OpenKNX/OpenKNX-KNeoPiX/Documentation/Renderings/rendered_case_Back.png

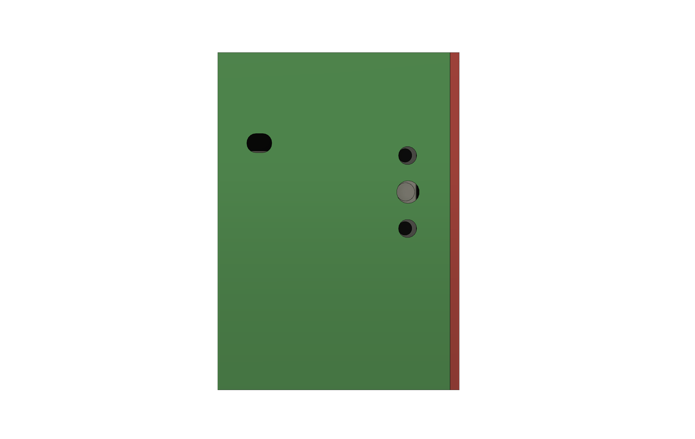
Documentation/Renderings/rendered_case_Back.png
