OpenKNX/OpenKNX-KNeoPiX/Documentation/Renderings/rendered_pcb_back.png

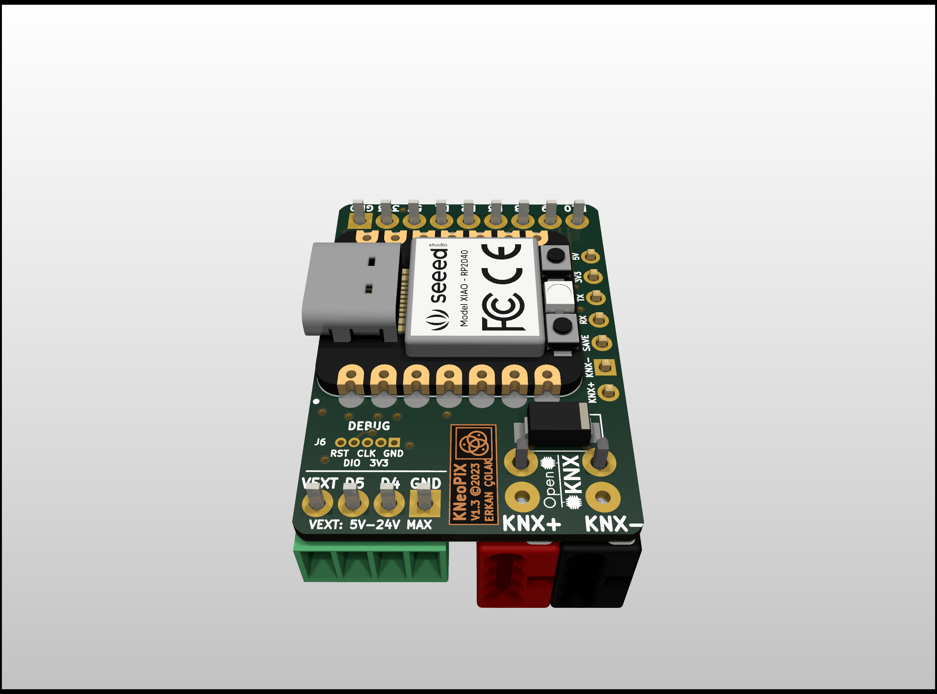
Documentation/Renderings/rendered_pcb_back.png
