OpenKNX/OpenKNX-KNeoPiX/Documentation/Renderings/rendered_pcb_bot.png

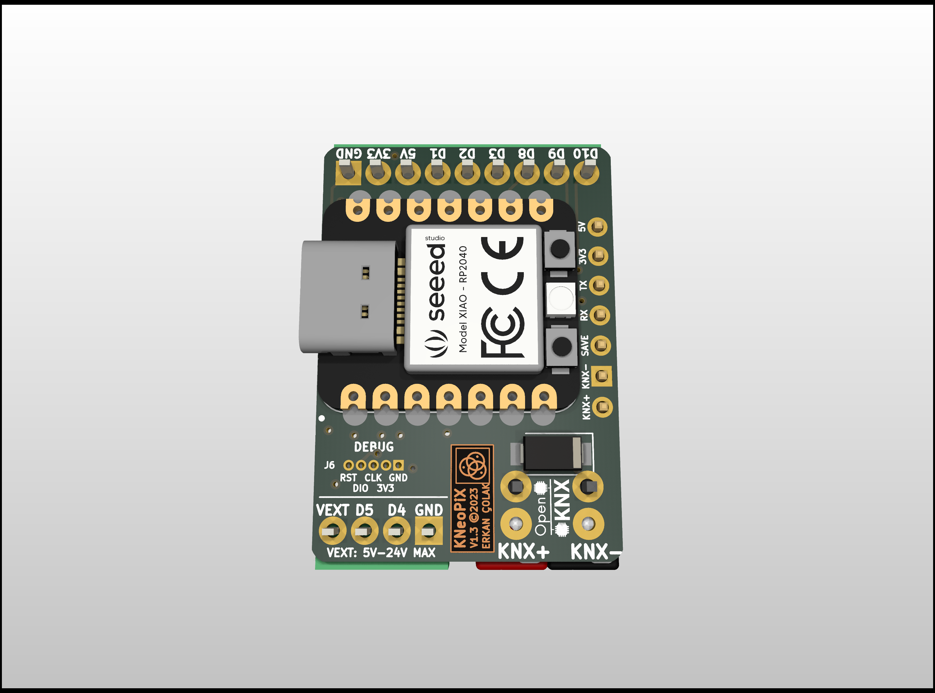
Documentation/Renderings/rendered_pcb_bot.png
