OpenKNX/OpenKNX-KNeoPiX/Documentation/Renderings/rendered_pcb_front.png

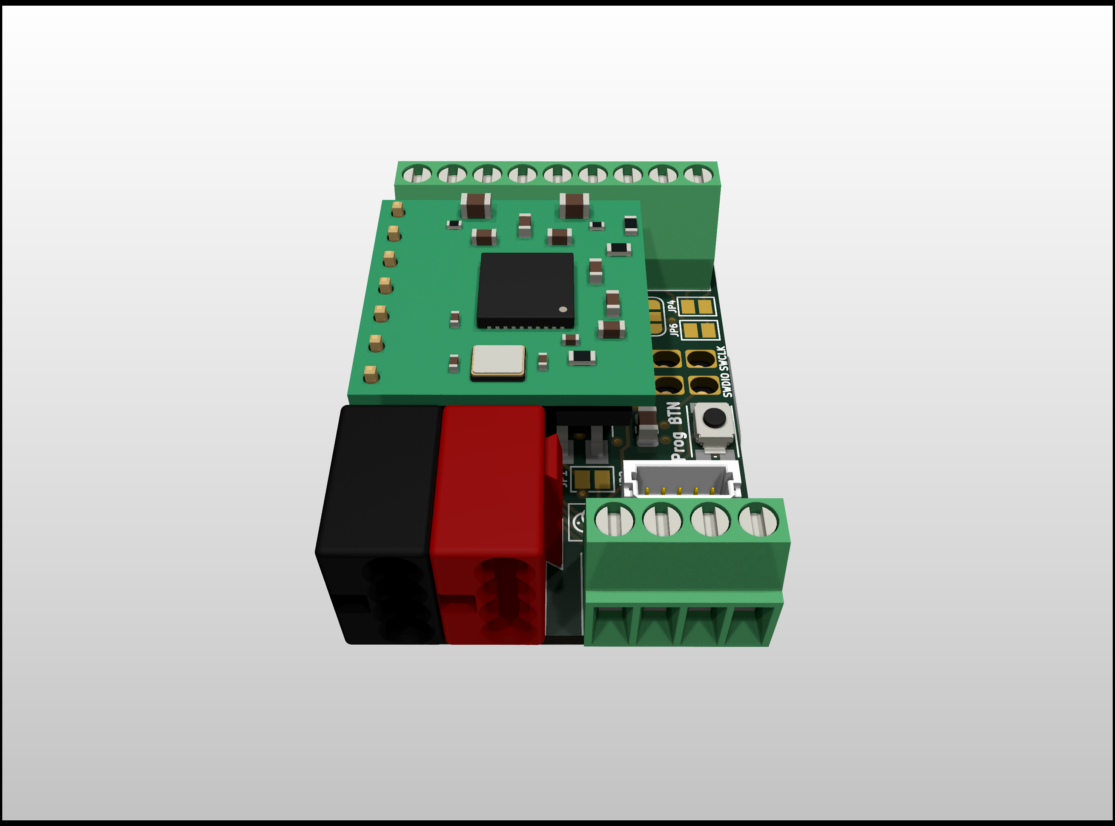
Documentation/Renderings/rendered_pcb_front.png
