OpenKNX/OpenKNX-KNeoPiX/Documentation/Renderings/rendered_pcb_l_back.png

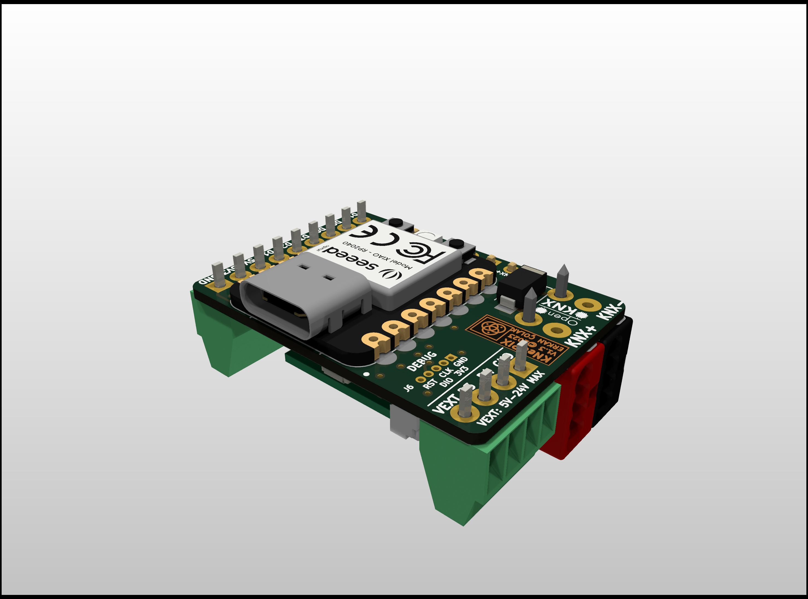
Documentation/Renderings/rendered_pcb_l_back.png
