OpenKNX/OpenKNX-KNeoPiX/Documentation/Renderings/rendered_pcb_l_front.png

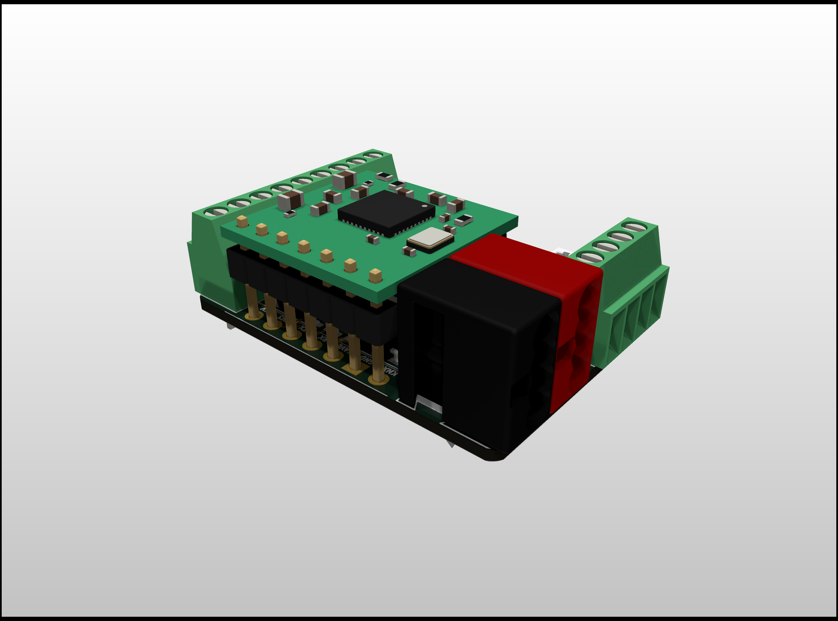
Documentation/Renderings/rendered_pcb_l_front.png
