OpenKNX/OpenKNX-KNeoPiX/Documentation/Renderings/rendered_pcb_r_back.png

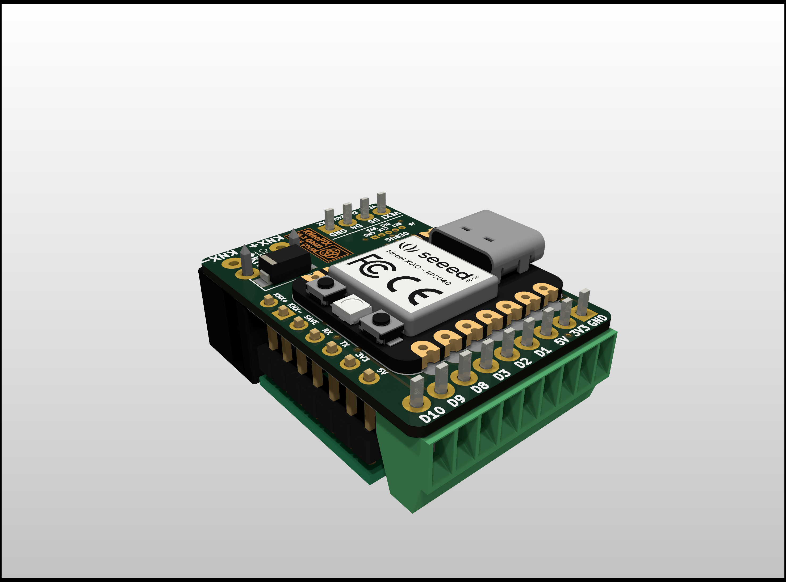
Documentation/Renderings/rendered_pcb_r_back.png
