OpenKNX/OpenKNX-KNeoPiX/Documentation/Renderings/rendered_pcb_r_front.png

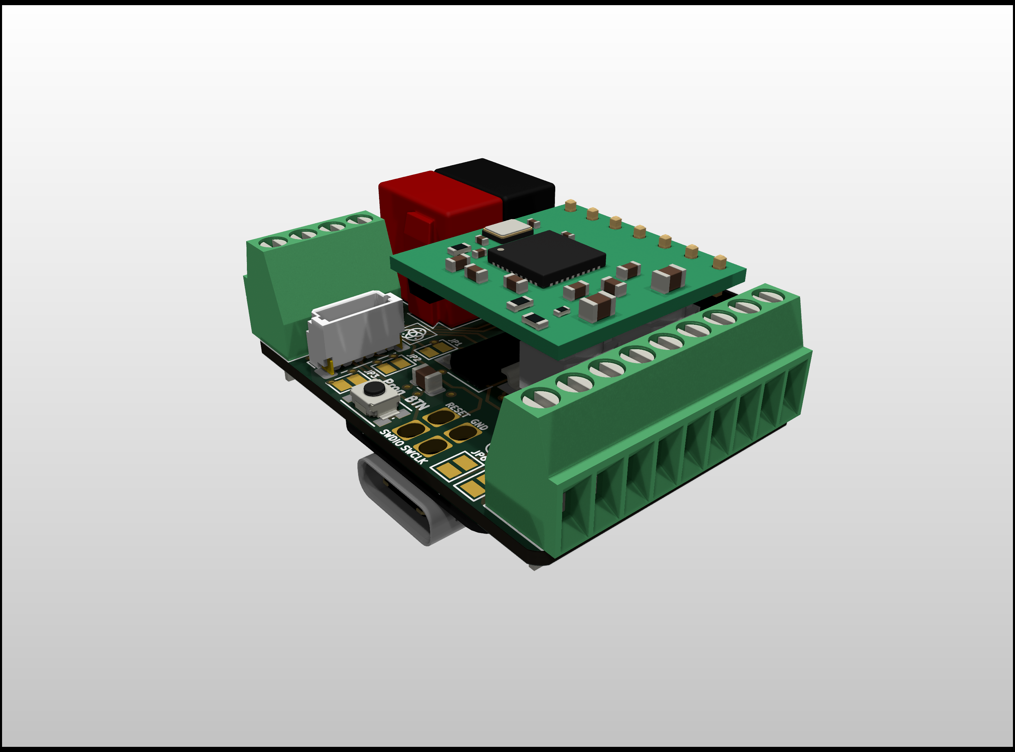
Documentation/Renderings/rendered_pcb_r_front.png
