OpenKNX/OpenKNX-KNeoPiX/Hardware/EDA-Files/Source/KNeoPix.3D-Models/TerminalBlock_Phoenix_MPT-0,5-4-2.54_1x04_P2.54mm_Horizontal.step

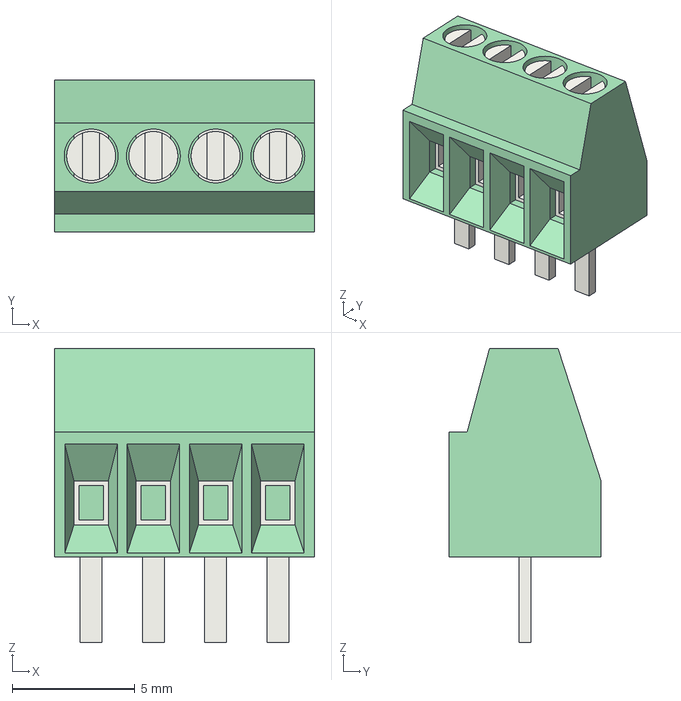
[picture p40: CAD file, 2023-09-03]
Hardware/EDA-Files/Source/KNeoPix.3D-Models/TerminalBlock_Phoenix_MPT-0,5-4-2.54_1x04_P2.54mm_Horizontal.step
10.6 x 6.20 x 12.0 mm
