OpenKNX/OpenKNX-KNeoPiX/Hardware/EDA-Files/Source/KNeoPix.3D-Models/NanoBCU_superflat_V00.11_wo_headers.step

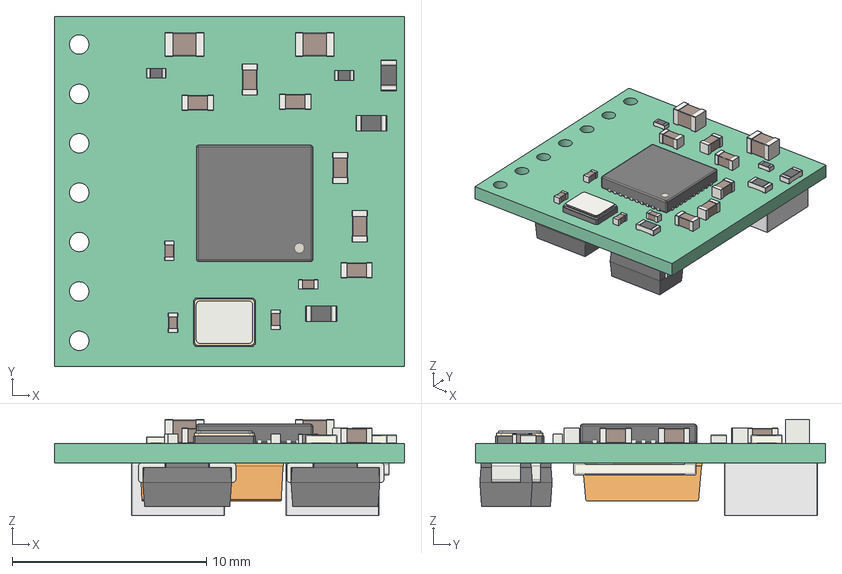
[picture p41: CAD file, 2023-09-03]
Hardware/EDA-Files/Source/KNeoPix.3D-Models/NanoBCU_superflat_V00.11_wo_headers.step
18.0 x 18.0 x 4.95 mm
Local_CS_8f96
Pcb_8f96
PCB_Sketch_8f96
C3_C_0603_1608Metric_5FFB0728
C2_C_0603_1608Metric_5F7CC168
R4_R_0603_1608Metric_5FFA04AE
C111_C_0805_2012Metric_5FFA3657
C101_C_0805_2012Metric_5FFA3646
C6_C_0402_1005Metric_5F7F7249
C5_C_0402_1005Metric_5F7CC1F8
C41_C_0603_1608Metric_5FACF283
R3_R_0402_1005Metric_5F7CC3D8
R2_R_0402_1005Metric_5F7CD3BF
C9_C_0402_1005Metric_5FFA6139
C8_C_0402_1005Metric_5FFA6163
C10_C_0603_1608Metric_5F7CC1C8
C11_C_0603_1608Metric_5F7E1A3A
R5_R_0603_1608Metric_5F7CC408
X1_Crystal_SMD_3225-4Pin_3.2x2.5mm_5F7CC372
U1_QFN-40-1EP_6x6mm_Pitch0.5mm_5F7D92D4
J3_R_0603_1608Metric_5F7CC258
C1_C_0603_1608Metric_5FFB093B
C4_0__Size4_5DADC971
L2_SRR4028_5F7CB1DF
L1_SRR4028_5FAB9F93
R1_R_2512_6332Metric_607A325D
D2_D_SMA_5F798DFE
D1_D_SMA_5F798D45
