OpenKNX/OpenKNX-KNeoPiX/Hardware/EDA-Files/Source/KNeoPix.3D-Models/SW_SPST_B3U-1000P.step

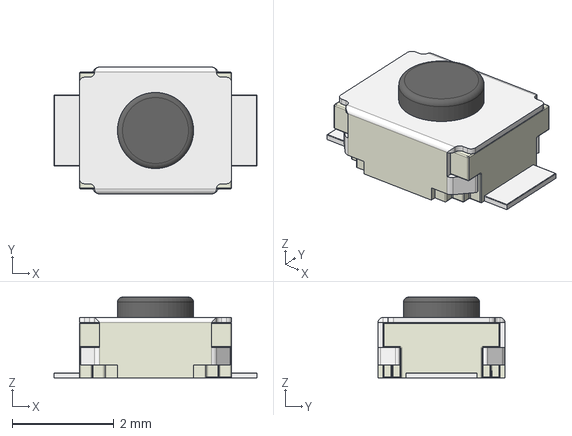
[picture p44: CAD file, 2023-09-03]
Hardware/EDA-Files/Source/KNeoPix.3D-Models/SW_SPST_B3U-1000P.step
4.00 x 2.50 x 1.59 mm
