OpenKNX/OpenKNX-KNeoPiX/Hardware/EDA-Files/Source/KNeoPix.3D-Models/User Library-DO-214AC(SMA).step

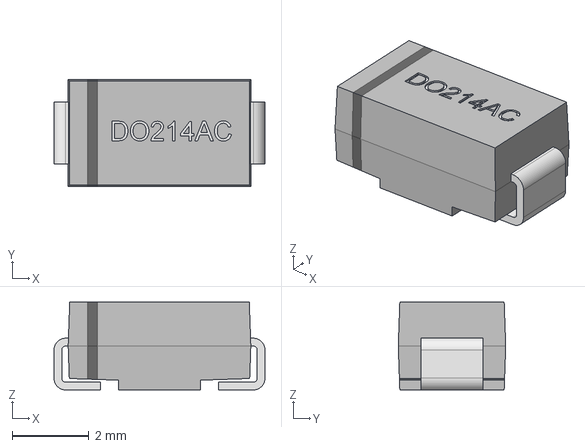
[picture p45: CAD file, 2023-09-03]
Hardware/EDA-Files/Source/KNeoPix.3D-Models/User Library-DO-214AC(SMA).step
5.49 x 2.79 x 2.29 mm
