OpenKNX/OpenKNX-KNeoPiX/Hardware/EDA-Files/Source/KNeoPix.3D-Models/MicroBCU2_V00.21_wo_headers.step

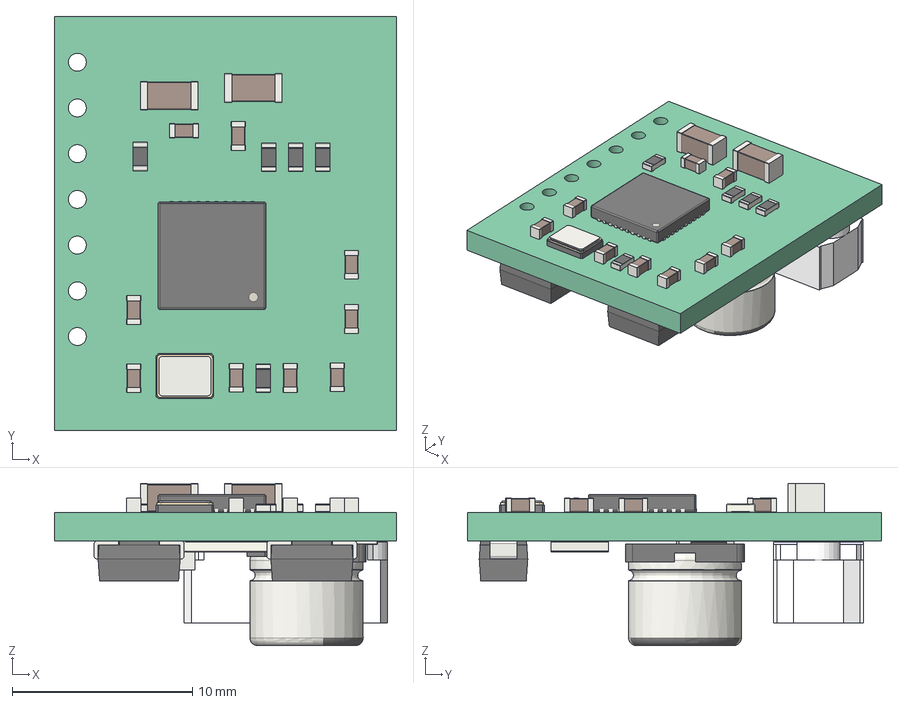
[picture p46: CAD file, 2023-09-03]
Hardware/EDA-Files/Source/KNeoPix.3D-Models/MicroBCU2_V00.21_wo_headers.step
19.0 x 23.0 x 9.00 mm
Local_CS_2c68
Pcb_2c68
PCB_Sketch_2c68
C111_C_1206_3216Metric_5FABA52C
C101_C_1206_3216Metric_5FAB98E7
C11_C_0603_1608Metric_5F7E1A3A
R5_R_0603_1608Metric_5F7CC408
X1_Crystal_SMD_3225-4Pin_3.2x2.5mm_5F7CC372
R4_R_0603_1608Metric_5F7CD09B
R3_R_0603_1608Metric_5F7CC3D8
U1_QFN-40-1EP_6x6mm_Pitch0.5mm_5F7D92D4
J3_R_0603_1608Metric_5F7CC258
R2_R_0603_1608Metric_5F7CD3BF
C9_C_0603_1608Metric_5F7CC108
C8_C_0603_1608Metric_5F7CC138
C10_C_0603_1608Metric_5F7CC1C8
C6_C_0603_1608Metric_5F7F7249
C5_C_0603_1608Metric_5F7CC1F8
C1_C_0603_1608Metric_5F7CC0D8
C2_C_0603_1608Metric_5F7CC168
C3_C_0603_1608Metric_5F7CC0A8
L2_vls5045ex_5F7CB1DF
L1_vls5045ex_5FAB9F93
C41_C_1206_3216Metric_5FACF283
R1_R_2512_6332Metric_5F7F71B4
D2_D_SMA_5F798DFE
D1_D_SMA_5F798D45
C4_CP_Elec_63x58_5DADC971
