OpenKNX/OpenKNX-KNeoPiX/Hardware/EDA-Files/Source/KNeoPix.3D-Models/W25Q128FWSIG_TR.STEP

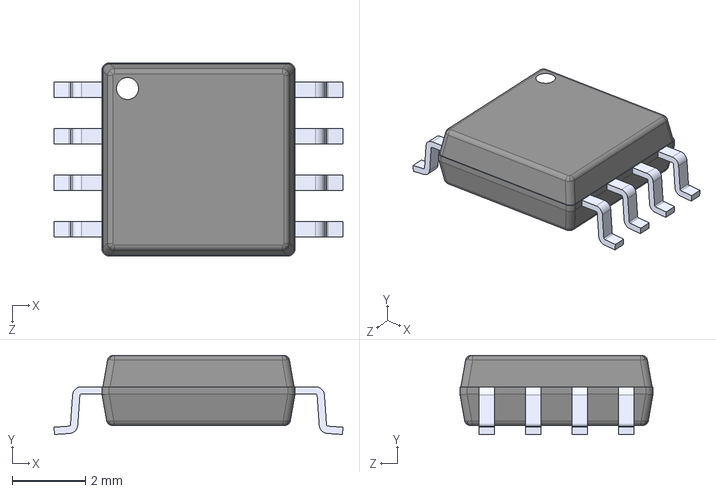
[picture p47: CAD file, 2023-09-03]
Hardware/EDA-Files/Source/KNeoPix.3D-Models/W25Q128FWSIG_TR.STEP
7.90 x 2.16 x 5.28 mm
