OpenKNX/OpenKNX-KNeoPiX/Hardware/EDA-Files/Source/KNeoPix.3D-Models/TerminalBlock_Phoenix_MPT-0,5-9-2.54_1x09_P2.54mm_Horizontal.step

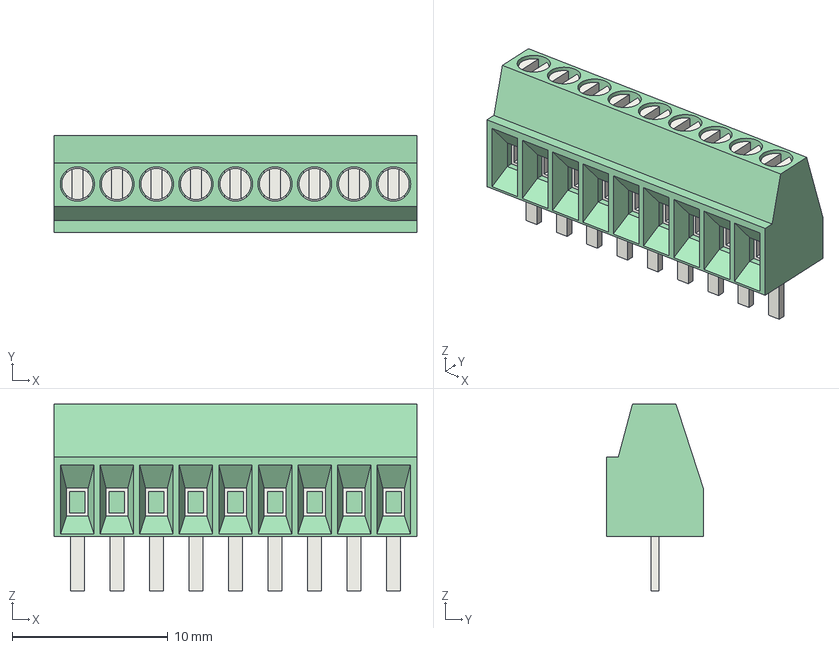
[picture p49: CAD file, 2023-09-03]
Hardware/EDA-Files/Source/KNeoPix.3D-Models/TerminalBlock_Phoenix_MPT-0,5-9-2.54_1x09_P2.54mm_Horizontal.step
23.3 x 6.20 x 12.0 mm
