OpenKNX/OpenKNX-KNeoPiX/Hardware/EDA-Files/Source/KNeoPix.3D-Models/USB4105-GF-A.stp

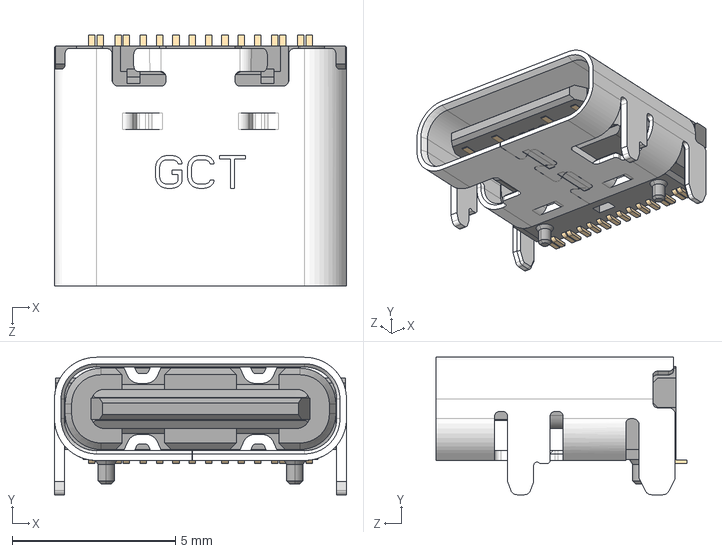
[picture p50: CAD file, 2023-09-03]
Hardware/EDA-Files/Source/KNeoPix.3D-Models/USB4105-GF-A.stp
8.94 x 4.21 x 7.70 mm
HSG_默认
