OpenKNX/OpenKNX-KNeoPiX/Hardware/EDA-Files/Source/KNeoPix.3D-Models/SC0915.step

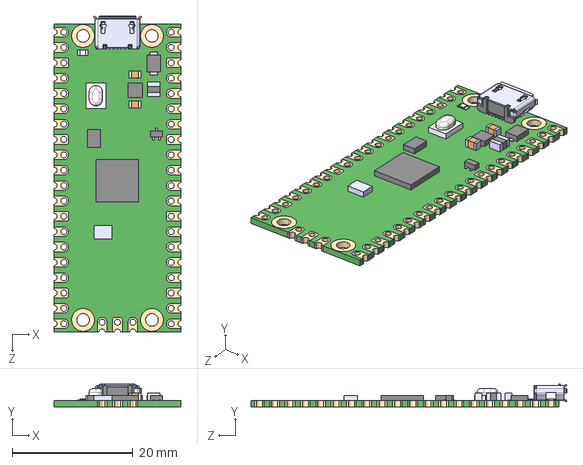
[picture p51: CAD file, 2023-09-03]
Hardware/EDA-Files/Source/KNeoPix.3D-Models/SC0915.step
21.0 x 3.73 x 52.3 mm
