OpenKNX/OpenKNX-KNeoPiX/Hardware/EDA-Files/Source/KNeoPix.3D-Models/SOT-223.step

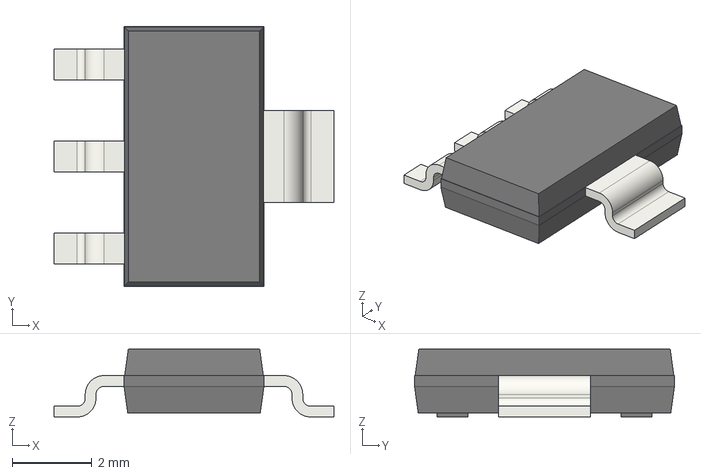
[picture p52: CAD file, 2023-09-03]
Hardware/EDA-Files/Source/KNeoPix.3D-Models/SOT-223.step
7.00 x 6.50 x 1.70 mm
