OpenKNX/OpenKNX-KNeoPiX/Hardware/EDA-Files/Source/KNeoPix.3D-Models/PinHeader_1x05_P2.54mm_Vertical.step

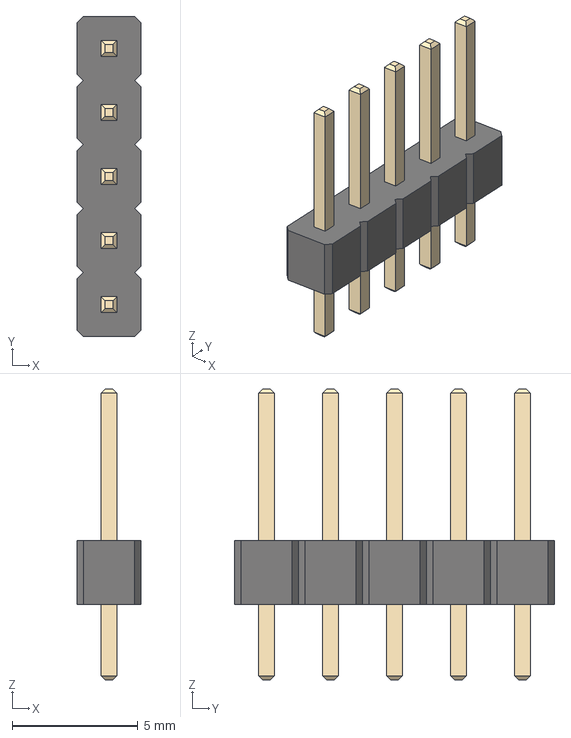
[picture p53: CAD file, 2023-09-03]
Hardware/EDA-Files/Source/KNeoPix.3D-Models/PinHeader_1x05_P2.54mm_Vertical.step
2.54 x 12.7 x 11.5 mm
