OpenKNX/OpenKNX-KNeoPiX/Hardware/EDA-Files/Source/KNeoPix.3D-Models/SOIC-8_3.9x4.9mm_P1.27mm.step

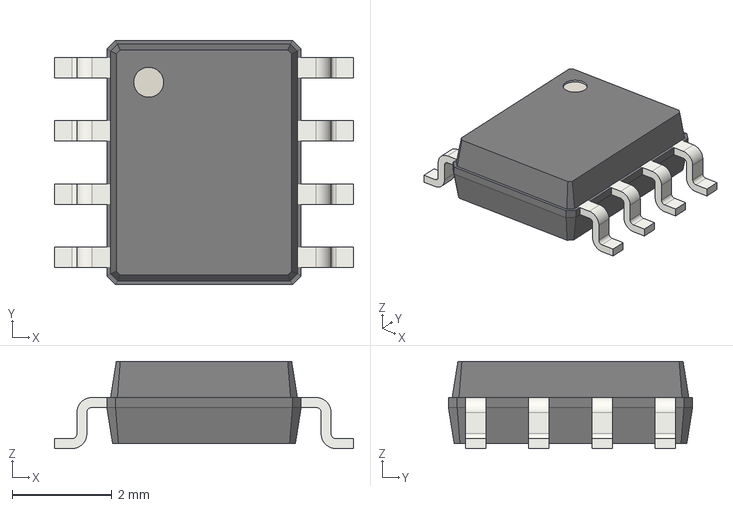
[picture p54: CAD file, 2023-09-03]
Hardware/EDA-Files/Source/KNeoPix.3D-Models/SOIC-8_3.9x4.9mm_P1.27mm.step
6.00 x 4.90 x 1.75 mm

Hardware/EDA-Files/Source/KNeoPix.3D-Models/R_0402_1005Metric.step
1.00 x 0.5 x 0.35 mm
