OpenKNX/OpenKNX-KNeoPiX/Hardware/EDA-Files/Source/KNeoPix.3D-Models/SW_SPST_B3U-1000P-B.step

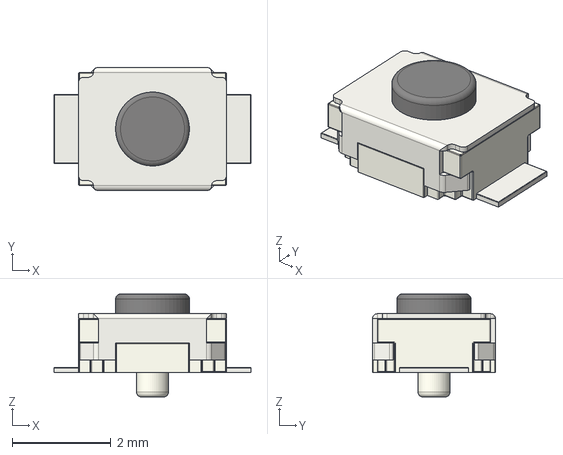
[picture p56: CAD file, 2023-09-03]
Hardware/EDA-Files/Source/KNeoPix.3D-Models/SW_SPST_B3U-1000P-B.step
4.00 x 2.50 x 2.09 mm
