OpenKNX/OpenKNX-KNeoPiX/Hardware/EDA-Files/Source/KNeoPix.3D-Models/Seeed Studio XIAO RP2040 v27.step

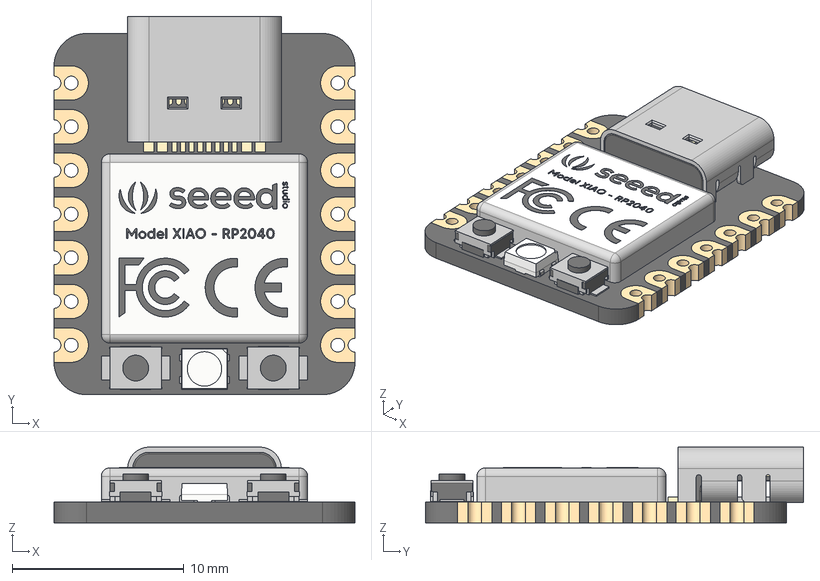
[picture p57: CAD file, 2023-09-03]
Hardware/EDA-Files/Source/KNeoPix.3D-Models/Seeed Studio XIAO RP2040 v27.step
17.5 x 22.0 x 4.41 mm
type-c v2
smd_button v3
DOUT
DIN
VSS
VDD
smd_button v3(Mirror)
