OpenKNX/OpenKNX-KNeoPiX/Hardware/EDA-Files/Source/KNeoPix.3D-Models/R_1206_3216Metric.step

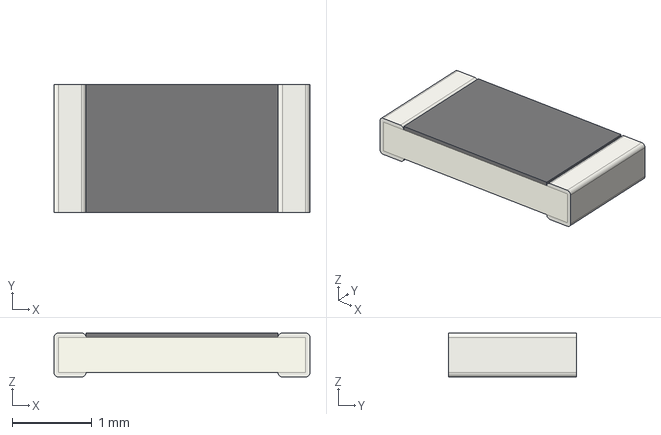
[picture p59: CAD file, 2023-09-03]
Hardware/EDA-Files/Source/KNeoPix.3D-Models/R_1206_3216Metric.step
3.20 x 1.60 x 0.55 mm
