OpenKNX/OpenKNX-KNeoPiX/Hardware/EDA-Files/Source/KNeoPix.3D-Models/PinSocket_1x10_P2.54mm_Vertical.step

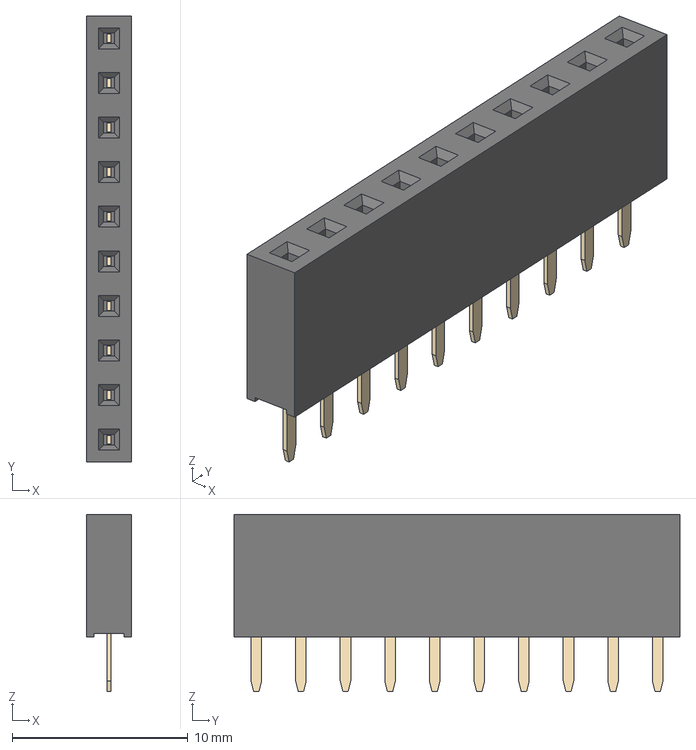
[picture p60: CAD file, 2023-09-03]
Hardware/EDA-Files/Source/KNeoPix.3D-Models/PinSocket_1x10_P2.54mm_Vertical.step
2.54 x 25.4 x 10.1 mm
