OpenKNX/OpenKNX-KNeoPiX/Hardware/EDA-Files/Source/KNeoPix.3D-Models/PinHeader_1x04_P2.54mm_Vertical.step

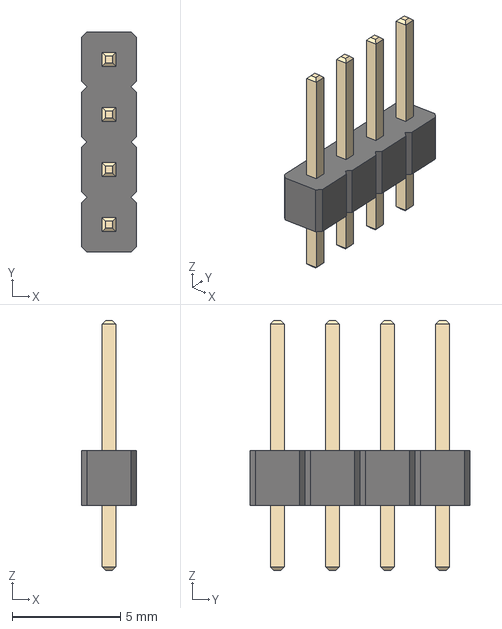
[picture p61: CAD file, 2023-09-03]
Hardware/EDA-Files/Source/KNeoPix.3D-Models/PinHeader_1x04_P2.54mm_Vertical.step
2.54 x 10.2 x 11.5 mm
