OpenKNX/OpenKNX-KNeoPiX/Hardware/EDA-Files/Source/KNeoPix.3D-Models/XIAO RP2040 v1.22.step

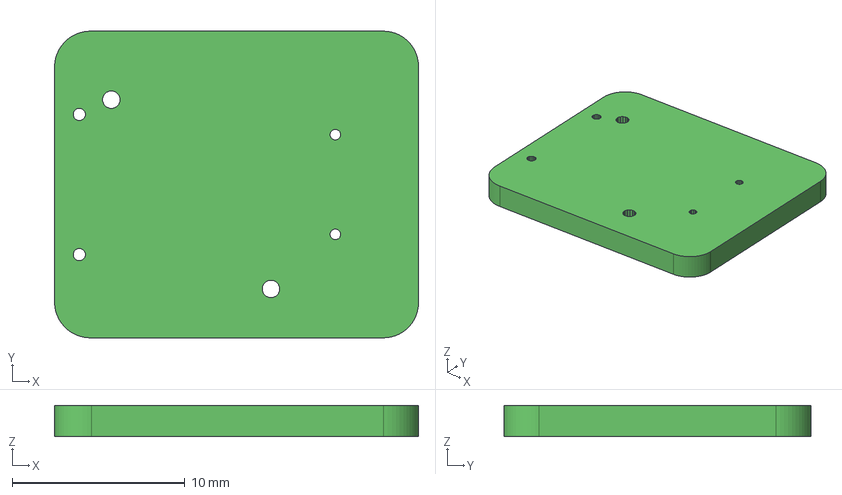
[picture p62: CAD file, 2023-09-03]
Hardware/EDA-Files/Source/KNeoPix.3D-Models/XIAO RP2040 v1.22.step
21.1 x 17.8 x 1.82 mm
