OpenKNX/OpenKNX-KNeoPiX/Hardware/EDA-Files/Source/KNeoPix.3D-Models/TerminalBlock_Phoenix_MPT-0,5-12-2.54_1x12_P2.54mm_Horizontal.step

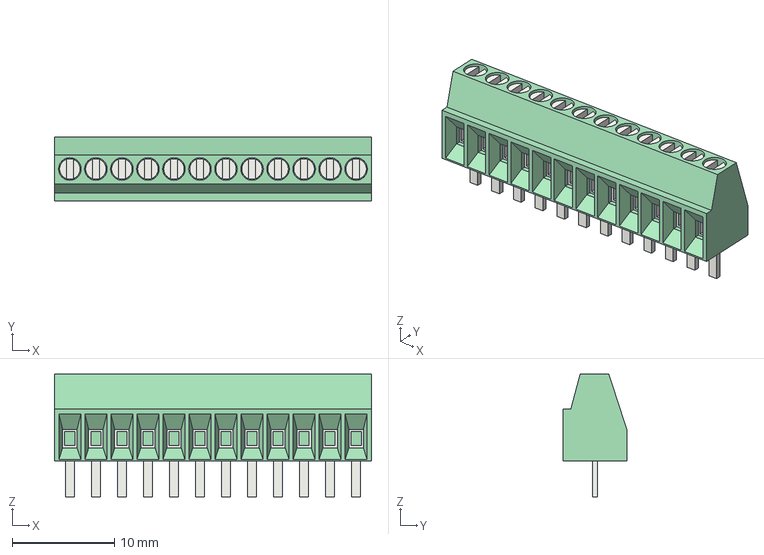
[picture p63: CAD file, 2023-09-03]
Hardware/EDA-Files/Source/KNeoPix.3D-Models/TerminalBlock_Phoenix_MPT-0,5-12-2.54_1x12_P2.54mm_Horizontal.step
30.9 x 6.20 x 12.0 mm
