OpenKNX/OpenKNX-KNeoPiX/Hardware/EDA-Files/Source/KNeoPix.3D-Models/243-212.stp

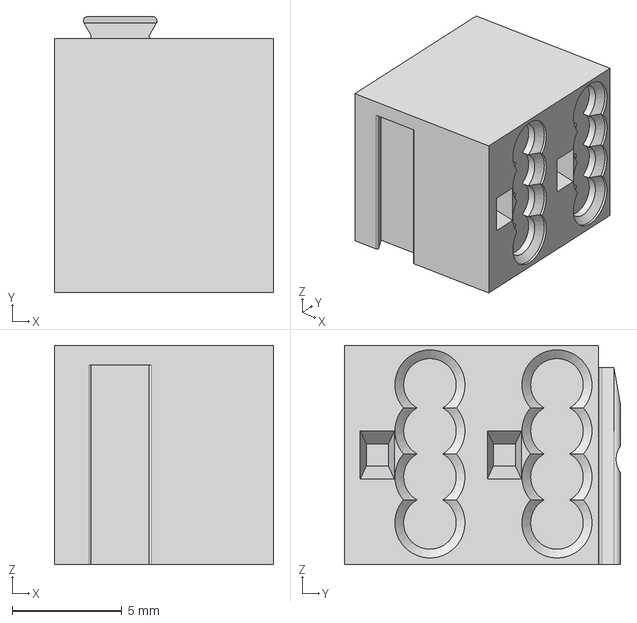
[picture p64: CAD file, 2023-09-03]
Hardware/EDA-Files/Source/KNeoPix.3D-Models/243-212.stp
10.0 x 12.6 x 10.0 mm
